hyano/pico-opm-writer/test/lfo_noise/result/wav_4a_01_am.tsv

file | mode | channel | sample_count | period_samples | cycle_count | confidence
wav_4a_01/am_nfrq_00_lfrq_00_kc_4a_mul_01.wav.zst | am | L | 7498868 | 262151.9194 | 28.6050 | 0.9948
wav_4a_01/am_nfrq_00_lfrq_01_kc_4a_mul_01.wav.zst | am | L | 7498868 | 262160.3223 | 28.6041 | 0.9950
wav_4a_01/am_nfrq_00_lfrq_02_kc_4a_mul_01.wav.zst | am | L | 7455437 | 262159.6877 | 28.4385 | 0.9949
wav_4a_01/am_nfrq_00_lfrq_03_kc_4a_mul_01.wav.zst | am | L | 7062996 | 262137.9389 | 26.9438 | 0.9949
wav_4a_01/am_nfrq_00_lfrq_04_kc_4a_mul_01.wav.zst | am | L | 6709862 | 262168.2118 | 25.5937 | 0.9949
wav_4a_01/am_nfrq_00_lfrq_05_kc_4a_mul_01.wav.zst | am | L | 6390348 | 262156.3210 | 24.3761 | 0.9950
wav_4a_01/am_nfrq_00_lfrq_06_kc_4a_mul_01.wav.zst | am | L | 6099892 | 262160.0876 | 23.2678 | 0.9950
wav_4a_01/am_nfrq_00_lfrq_07_kc_4a_mul_01.wav.zst | am | L | 5834681 | 262156.3415 | 22.2565 | 0.9949
wav_4a_01/am_nfrq_00_lfrq_08_kc_4a_mul_01.wav.zst | am | L | 5591530 | 262157.6165 | 21.3289 | 0.9950
wav_4a_01/am_nfrq_00_lfrq_09_kc_4a_mul_01.wav.zst | am | L | 5367877 | 262171.0440 | 20.4747 | 0.9950
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
