hyano/pico-opm-writer/test/lfo_noise/result/wav_4a_01_pm.tsv

file | mode | channel | sample_count | period_samples | cycle_count | confidence
wav_4a_01/pm_nfrq_00_lfrq_00_kc_4a_mul_01.wav.zst | pm | L | 7498867 | 262137.6661 | 28.6066 | 0.9910
wav_4a_01/pm_nfrq_00_lfrq_01_kc_4a_mul_01.wav.zst | pm | L | 7498867 | 262142.3183 | 28.6061 | 0.9905
wav_4a_01/pm_nfrq_00_lfrq_02_kc_4a_mul_01.wav.zst | pm | L | 7455435 | 262142.2755 | 28.4404 | 0.9905
wav_4a_01/pm_nfrq_00_lfrq_03_kc_4a_mul_01.wav.zst | pm | L | 7062993 | 262129.4264 | 26.9447 | 0.9868
wav_4a_01/pm_nfrq_00_lfrq_04_kc_4a_mul_01.wav.zst | pm | L | 6709856 | 262127.8747 | 25.5976 | 0.9906
wav_4a_01/pm_nfrq_00_lfrq_05_kc_4a_mul_01.wav.zst | pm | L | 6390348 | 262146.9127 | 24.3770 | 0.9892
wav_4a_01/pm_nfrq_00_lfrq_06_kc_4a_mul_01.wav.zst | pm | L | 6099892 | 262122.1143 | 23.2712 | 0.9888
wav_4a_01/pm_nfrq_00_lfrq_07_kc_4a_mul_01.wav.zst | pm | L | 5834682 | 262126.6337 | 22.2590 | 0.9898
wav_4a_01/pm_nfrq_00_lfrq_08_kc_4a_mul_01.wav.zst | pm | L | 5591531 | 262135.2868 | 21.3307 | 0.9909
wav_4a_01/pm_nfrq_00_lfrq_09_kc_4a_mul_01.wav.zst | pm | L | 5367877 | 262142.4000 | 20.4770 | 0.9900
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
