hyano/pico-opm-writer/test/lfo_noise/result/wav_am.tsv

file | mode | channel | sample_count | period_samples | cycle_count | confidence
wav/am_nfrq_00_lfrq_00_kc_4a_mul_04.wav.zst | am | L | 7498868 | 262137.4021 | 28.6066 | 0.9947
wav/am_nfrq_00_lfrq_01_kc_4a_mul_04.wav.zst | am | L | 7498868 | 262153.5946 | 28.6049 | 0.9950
wav/am_nfrq_00_lfrq_02_kc_4a_mul_04.wav.zst | am | L | 7455437 | 262135.8975 | 28.4411 | 0.9946
wav/am_nfrq_00_lfrq_03_kc_4a_mul_04.wav.zst | am | L | 7062996 | 262159.6973 | 26.9416 | 0.9948
wav/am_nfrq_00_lfrq_04_kc_4a_mul_04.wav.zst | am | L | 6709862 | 262164.9075 | 25.5941 | 0.9949
wav/am_nfrq_00_lfrq_05_kc_4a_mul_04.wav.zst | am | L | 6390348 | 262144.8821 | 24.3772 | 0.9949
wav/am_nfrq_00_lfrq_06_kc_4a_mul_04.wav.zst | am | L | 6099891 | 262163.5428 | 23.2675 | 0.9950
wav/am_nfrq_00_lfrq_07_kc_4a_mul_04.wav.zst | am | L | 5834682 | 262140.6615 | 22.2578 | 0.9949
wav/am_nfrq_00_lfrq_08_kc_4a_mul_04.wav.zst | am | L | 5591531 | 262159.3421 | 21.3287 | 0.9948
wav/am_nfrq_00_lfrq_09_kc_4a_mul_04.wav.zst | am | L | 5367877 | 262144.8064 | 20.4768 | 0.9947
wav/am_nfrq_00_lfrq_0a_kc_4a_mul_04.wav.zst | am | L | 5161471 | 262168.3591 | 19.6876 | 0.9949
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
