hyano/pico-opm-writer/test/lfo_noise/result/wav_lfrq28_am.tsv

file | mode | channel | sample_count | period_samples | cycle_count | confidence
wav_lfrq28/am_nfrq_00_lfrq_24_kc_4a_mul_04.wav.zst | am | L | 7498868 | 65536.2807 | 114.4232 | 0.9133
wav_lfrq28/am_nfrq_00_lfrq_25_kc_4a_mul_04.wav.zst | am | L | 7498867 | 65536.6209 | 114.4225 | 0.8626
wav_lfrq28/am_nfrq_00_lfrq_26_kc_4a_mul_04.wav.zst | am | L | 7498867 | 65536.7708 | 114.4223 | 0.8609
wav_lfrq28/am_nfrq_00_lfrq_27_kc_4a_mul_04.wav.zst | am | L | 7498867 | 65536.5741 | 114.4226 | 0.8626
wav_lfrq28/am_nfrq_00_lfrq_28_kc_4a_mul_04.wav.zst | am | L | 7498867 | 65536.7278 | 114.4224 | 0.8582
wav_lfrq28/am_nfrq_00_lfrq_29_kc_4a_mul_04.wav.zst | am | L | 7498868 | 65536.2855 | 114.4231 | 0.8591
wav_lfrq28/am_nfrq_00_lfrq_2a_kc_4a_mul_04.wav.zst | am | L | 7498868 | 65536.2191 | 114.4233 | 0.9086
wav_lfrq28/am_nfrq_00_lfrq_2b_kc_4a_mul_04.wav.zst | am | L | 7498867 | 65536.3893 | 114.4230 | 0.8583
wav_lfrq28/am_nfrq_00_lfrq_2c_kc_4a_mul_04.wav.zst | am | L | 7498868 | 65536.7194 | 114.4224 | 0.8617
wav_lfrq28/am_nfrq_1f_lfrq_24_kc_4a_mul_04.wav.zst | am | L | 7498867 | 65536.1403 | 114.4234 | 0.6660
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
