hyano/pico-opm-writer/src/stats.c

/*
 * 実行時リソース使用量の計測の実装
 *
 * SPDX-License-Identifier: MIT
 */
#include "stats.h"

#include "pico/stdlib.h"

/* ---- 1 秒窓管理 --------------------------------------------------------- */

static struct
{
    uint32_t window_start_us;  /* 現在の窓の開始時刻 [us] */
    uint32_t busy_us;          /* 窓内でサービス関数の中に居た時間 [us] */
    uint32_t usb_busy_us;      /* 窓内で tud_task() の中に居た時間 [us] */
    uint64_t frames_in_window; /* 窓内で追加されたフレーム数 */
    uint32_t passes_in_window; /* 窓内のメインループ周回数 */
} s_window = {
    .window_start_us = 0,
    .busy_us = 0,
    .usb_busy_us = 0,
    .frames_in_window = 0,
    .passes_in_window = 0,
};

/* 直近窓のメインループ周回数 [passes/s] */
static uint32_t s_loop_rate;

/* ---- サービスごとの実仕事率 -------------------------------------------- */

/* 窓の中の生カウント。窓が閉じたときに 1 秒あたりへ直して s_svc へ移す。 */
static struct
{
    uint32_t calls;
    uint32_t worked;
#if STATS_PROFILE
    uint32_t busy_us;
#endif
} s_svc_win[STATS_SVC_COUNT];

/* 直近窓の確定値 [回/s] */
static struct
{
    uint32_t calls;
    uint32_t worked;
#if STATS_PROFILE
    uint32_t busy_us;
#endif
} s_svc[STATS_SVC_COUNT];

/* `s` の 1 行に 6 個並べるので短くする */
static const char *const SVC_NAME[STATS_SVC_COUNT] = {
    [STATS_SVC_PCM8] = "pcm8",
    [STATS_SVC_CAPTURE] = "cap",
    [STATS_SVC_I2S] = "i2s",
    [STATS_SVC_VGM] = "vgm",
    [STATS_SVC_MDX] = "mdx",
    [STATS_SVC_STORAGE] = "sto",
};

void stats_svc_note(stats_svc_t svc, bool worked)
{
    s_svc_win[svc].calls++;
    if (worked)
    {
        s_svc_win[svc].worked++;
    }
}

#if STATS_PROFILE
void stats_svc_busy_add(stats_svc_t svc, uint32_t us)
{
    s_svc_win[svc].busy_us += us;
}

uint32_t stats_svc_busy_us(stats_svc_t svc)
{
    return s_svc[svc].busy_us;
}
#endif

uint32_t stats_svc_calls(stats_svc_t svc)
{
    return s_svc[svc].calls;
}

uint32_t stats_svc_worked(stats_svc_t svc)
{
    return s_svc[svc].worked;
}

const char *stats_svc_name(stats_svc_t svc)
{
    return SVC_NAME[svc];
}

/* 窓が閉じたときに 1 秒あたりへ直す。窓は 1 秒ちょうどとは限らない。 */
static void svc_close_window(uint32_t elapsed_us)
{
    for (uint32_t i = 0; i < (uint32_t)STATS_SVC_COUNT; i++)
    {
        s_svc[i].calls =
            (uint32_t)(((uint64_t)s_svc_win[i].calls * 1000000u) / elapsed_us);
        s_svc[i].worked =
            (uint32_t)(((uint64_t)s_svc_win[i].worked * 1000000u) / elapsed_us);
#if STATS_PROFILE
        s_svc[i].busy_us =
            (uint32_t)(((uint64_t)s_svc_win[i].busy_us * 1000000u) / elapsed_us);
#endif
        s_svc_win[i].calls = 0;
        s_svc_win[i].worked = 0;
#if STATS_PROFILE
        s_svc_win[i].busy_us = 0;
#endif
    }
}

/* 起動時と `s 0` で全部 0 に戻す */
static void svc_clear(void)
{
    for (uint32_t i = 0; i < (uint32_t)STATS_SVC_COUNT; i++)
    {
        s_svc_win[i].calls = 0;
        s_svc_win[i].worked = 0;
        s_svc[i].calls = 0;
        s_svc[i].worked = 0;
#if STATS_PROFILE
        s_svc_win[i].busy_us = 0;
        s_svc[i].busy_us = 0;
#endif
    }
}

/* ---- CPU 使用率 -------------------------------------------------------- */

static struct
{
    uint32_t cpu_percent;     /* 直近窓の CPU 使用率 [%] */
    uint32_t cpu_percent_max; /* リセット以降の最大値 [%] */
    uint32_t usb_percent;     /* 直近窓の tud_task() の占有率 [%] */
} s_cpu = {
    .cpu_percent = 0,
    .cpu_percent_max = 0,
    .usb_percent = 0,
};

/* ---- DMA リング -------------------------------------------------------- */

static struct
{
    uint32_t frames_current; /* 現在の未処理フレーム数 */
    uint32_t frames_max;     /* リセット以降の最大値 */
} s_ring = {
    .frames_current = 0,
    .frames_max = 0,
};

/* ---- USB TX ------------------------------------------------------------ */

static struct
{
    uint32_t bytes_current; /* 現在の滞留バイト数 */
    uint32_t bytes_max;     /* リセット以降の最大値 */
} s_usb_tx = {
    .bytes_current = 0,
    .bytes_max = 0,
};

/* ---- I2S 出力 ---------------------------------------------------------- */

/*
 * こちらは減る方向が危険なので low-water を残す。UINT32_MAX は「まだ 1 度も
 * 通知されていない」ことを表す番兵。
 */
static struct
{
    uint32_t depth_current; /* 現在の先行フレーム数 */
    uint32_t depth_min;     /* リセット以降の最小値 */
} s_i2s = {
    .depth_current = 0,
    .depth_min = UINT32_MAX,
};

/* ---- カウンタ ---------------------------------------------------------- */

static struct
{
    uint32_t overrun;      /* DMA overrun 発生回数 */
    uint64_t forbidden;    /* 禁止コード E=0 の検出数 */
    uint32_t rxstall;      /* PIO RX FIFO あふれ回数 */
    uint64_t frames;       /* 総フレーム数 */
    uint32_t frame_rate;   /* 直近窓でのフレームレート [frames/s] */
    uint32_t i2s_underrun; /* I2S の先行分が尽きた回数 */
    uint64_t pcm_clip;     /* ADPCM を混ぜた結果あふれたサンプル数 */
} s_counters = {
    .overrun = 0,
    .forbidden = 0,
    .rxstall = 0,
    .frames = 0,
    .frame_rate = 0,
    .i2s_underrun = 0,
    .pcm_clip = 0,
};

/* ---- フラッシュ書き込み / VGM ------------------------------------------ */

static struct
{
    uint32_t flash_write;           /* 4KiB ブロックの書き出し回数 */
    uint32_t flash_blackout_max_us; /* 書き出しでメインループが止まった最大時間 */
    uint32_t seq_lag_max_us;        /* シーケンサの遅れの最大値 */
    uint32_t loop_period_max_us;    /* service_all() の呼び出し間隔の最大値 */
    uint32_t audio_gap_max_us;      /* 音声チェーンが回った間隔の最大値 */
} s_ext = {
    .flash_write = 0,
    .flash_blackout_max_us = 0,
    .seq_lag_max_us = 0,
    .loop_period_max_us = 0,
    .audio_gap_max_us = 0,
};

/* ---- OPM バス（STATS_PROFILE のみ）------------------------------------- */

#if STATS_PROFILE
/* 窓の中の生カウント。窓が閉じたときに 1 秒あたりへ直して s_opm へ移す。 */
static struct
{
    uint32_t writes;
    uint32_t busy_us;
} s_opm_win;

static struct
{
    uint32_t writes;  /* 直近窓の書き込み回数 [writes/s] */
    uint32_t busy_us; /* 直近窓の滞在時間 [us/s] */
    uint32_t max_us;  /* リセット以降の 1 回の最大値 [us] */
} s_opm;
#endif

/* 起動時と `s 0` で 0 に戻す。STATS_PROFILE=0 では何も持たないので空になる。 */
static void opm_clear_stats(void)
{
#if STATS_PROFILE
    s_opm_win.writes = 0;
    s_opm_win.busy_us = 0;
    s_opm.writes = 0;
    s_opm.busy_us = 0;
    s_opm.max_us = 0;
#endif
}

/* ---- CPU 使用率 -------------------------------------------------------- */

void stats_busy_add(uint32_t busy_us)
{
    s_window.busy_us += busy_us;
}

void stats_usb_busy_add(uint32_t busy_us)
{
    s_window.usb_busy_us += busy_us;
}

void stats_service(void)
{
    s_window.passes_in_window++;

    uint32_t now_us = time_us_32();
    uint32_t elapsed_us = now_us - s_window.window_start_us;

    /* 1 秒 (1000000us) に満たなければ何もしない */
    if (elapsed_us < 1000000u)
    {
        return;
    }

    /* 窓が閉じた。統計を計算する。 */

    /* CPU 使用率を計算。窓は 1 秒ちょうどとは限らないので実経過時間で割る。 */
    uint32_t cpu_pct = (uint32_t)(((uint64_t)s_window.busy_us * 100u) / elapsed_us);
    if (cpu_pct > 100u)
    {
        cpu_pct = 100u;
    }
    s_cpu.cpu_percent = cpu_pct;

    /* 最大値を更新 */
    if (cpu_pct > s_cpu.cpu_percent_max)
    {
        s_cpu.cpu_percent_max = cpu_pct;
    }

    uint32_t usb_pct = (uint32_t)(((uint64_t)s_window.usb_busy_us * 100u) / elapsed_us);
    s_cpu.usb_percent = (usb_pct > 100u) ? 100u : usb_pct;

    /* フレームレートを計算（frames/s） */
    uint32_t frame_rate = (uint32_t)((s_window.frames_in_window * 1000000u) / elapsed_us);
    s_counters.frame_rate = frame_rate;

    /* メインループの周回数（1 周あたりの固定費を見積もるのに使う） */
    s_loop_rate = (uint32_t)(((uint64_t)s_window.passes_in_window * 1000000u) / elapsed_us);

    /* サービスごとの呼び出し回数と実仕事回数 */
    svc_close_window(elapsed_us);

#if STATS_PROFILE
    /* OPM バスも同じく 1 秒あたりへ直す（最大値は窓をまたいで残す） */
    s_opm.writes = (uint32_t)(((uint64_t)s_opm_win.writes * 1000000u) / elapsed_us);
    s_opm.busy_us = (uint32_t)(((uint64_t)s_opm_win.busy_us * 1000000u) / elapsed_us);
    s_opm_win.writes = 0;
    s_opm_win.busy_us = 0;
#endif

    /* 次の窓へ */
    s_window.window_start_us = now_us;
    s_window.busy_us = 0;
    s_window.usb_busy_us = 0;
    s_window.frames_in_window = 0;
    s_window.passes_in_window = 0;
}

uint32_t stats_loop_rate(void)
{
    return s_loop_rate;
}

uint32_t stats_usb_percent(void)
{
    return s_cpu.usb_percent;
}

uint32_t stats_cpu_percent(void)
{
    return s_cpu.cpu_percent;
}

uint32_t stats_cpu_percent_max(void)
{
    return s_cpu.cpu_percent_max;
}

/* ---- DMA リング -------------------------------------------------------- */

void stats_ring_update(uint32_t unread_frames)
{
    s_ring.frames_current = unread_frames;
    if (unread_frames > s_ring.frames_max)
    {
        s_ring.frames_max = unread_frames;
    }
}

uint32_t stats_ring_frames(void)
{
    return s_ring.frames_current;
}

uint32_t stats_ring_frames_max(void)
{
    return s_ring.frames_max;
}

/* ---- USB TX ------------------------------------------------------------ */

void stats_usb_tx_update(uint32_t pending_bytes)
{
    s_usb_tx.bytes_current = pending_bytes;
    if (pending_bytes > s_usb_tx.bytes_max)
    {
        s_usb_tx.bytes_max = pending_bytes;
    }
}

uint32_t stats_usb_tx_bytes(void)
{
    return s_usb_tx.bytes_current;
}

uint32_t stats_usb_tx_bytes_max(void)
{
    return s_usb_tx.bytes_max;
}

/* ---- I2S 出力 ---------------------------------------------------------- */

void __not_in_flash_func(stats_i2s_update)(uint32_t depth_frames)
{
    s_i2s.depth_current = depth_frames;
    if (depth_frames < s_i2s.depth_min)
    {
        s_i2s.depth_min = depth_frames;
    }
}

uint32_t stats_i2s_depth(void)
{
    return s_i2s.depth_current;
}

uint32_t stats_i2s_depth_min(void)
{
    return s_i2s.depth_min;
}

/* ---- カウンタ ---------------------------------------------------------- */

void stats_count_overrun(void)
{
    s_counters.overrun++;
}

void __not_in_flash_func(stats_count_forbidden)(uint32_t n)
{
    s_counters.forbidden += n;
}

void stats_count_rxstall(void)
{
    s_counters.rxstall++;
}

void stats_count_frames(uint32_t n)
{
    s_counters.frames += n;
    s_window.frames_in_window += n;
}

void __not_in_flash_func(stats_count_i2s_underrun)(void)
{
    s_counters.i2s_underrun++;
}

void __not_in_flash_func(stats_count_pcm_clip)(uint32_t n)
{
    s_counters.pcm_clip += n;
}

uint32_t stats_overrun(void)
{
    return s_counters.overrun;
}

uint64_t stats_forbidden(void)
{
    return s_counters.forbidden;
}

uint32_t stats_rxstall(void)
{
    return s_counters.rxstall;
}

uint64_t stats_frames(void)
{
    return s_counters.frames;
}

uint32_t stats_i2s_underrun(void)
{
    return s_counters.i2s_underrun;
}

uint64_t stats_pcm_clip(void)
{
    return s_counters.pcm_clip;
}

uint32_t stats_frame_rate(void)
{
    return s_counters.frame_rate;
}

/* ---- フラッシュ書き込み ------------------------------------------------ */

void stats_count_flash_write(void)
{
    s_ext.flash_write++;
}

void stats_flash_blackout_add(uint32_t us)
{
    if (us > s_ext.flash_blackout_max_us)
    {
        s_ext.flash_blackout_max_us = us;
    }
}

uint32_t stats_flash_write(void)
{
    return s_ext.flash_write;
}

uint32_t stats_flash_blackout_max_us(void)
{
    return s_ext.flash_blackout_max_us;
}

/* ---- シーケンサ再生 (VGM / MDX で共用) ---------------------------------- */

void stats_seq_lag_update(uint32_t us)
{
    if (us > s_ext.seq_lag_max_us)
    {
        s_ext.seq_lag_max_us = us;
    }
}

uint32_t stats_seq_lag_max_us(void)
{
    return s_ext.seq_lag_max_us;
}

/* ---- メインループの周期 ------------------------------------------------ */

void __not_in_flash_func(stats_loop_period_add)(uint32_t us)
{
    if (us > s_ext.loop_period_max_us)
    {
        s_ext.loop_period_max_us = us;
    }
}

void __not_in_flash_func(stats_audio_gap_add)(uint32_t us)
{
    if (us > s_ext.audio_gap_max_us)
    {
        s_ext.audio_gap_max_us = us;
    }
}

uint32_t stats_loop_period_max_us(void)
{
    return s_ext.loop_period_max_us;
}

uint32_t stats_audio_gap_max_us(void)
{
    return s_ext.audio_gap_max_us;
}

/* ---- OPM バス ---------------------------------------------------------- */

#if STATS_PROFILE
void stats_opm_write_add(uint32_t us)
{
    s_opm_win.writes++;
    s_opm_win.busy_us += us;
    if (us > s_opm.max_us)
    {
        s_opm.max_us = us;
    }
}

uint32_t stats_opm_writes(void)
{
    return s_opm.writes;
}

uint32_t stats_opm_write_us(void)
{
    return s_opm.busy_us;
}

uint32_t stats_opm_write_max_us(void)
{
    return s_opm.max_us;
}
#endif

/* ---- 初期化・リセット -------------------------------------------------- */

void stats_init(void)
{
    svc_clear();

    s_window.window_start_us = time_us_32();
    s_window.busy_us = 0;
    s_window.frames_in_window = 0;

    s_cpu.cpu_percent = 0;
    s_cpu.cpu_percent_max = 0;

    s_ring.frames_current = 0;
    s_ring.frames_max = 0;

    s_usb_tx.bytes_current = 0;
    s_usb_tx.bytes_max = 0;

    s_i2s.depth_current = 0;
    s_i2s.depth_min = UINT32_MAX;

    s_counters.overrun = 0;
    s_counters.forbidden = 0;
    s_counters.rxstall = 0;
    s_counters.frames = 0;
    s_counters.frame_rate = 0;
    s_counters.i2s_underrun = 0;
    s_counters.pcm_clip = 0;

    s_ext.flash_write = 0;
    s_ext.flash_blackout_max_us = 0;
    s_ext.seq_lag_max_us = 0;
    s_ext.loop_period_max_us = 0;
    s_ext.audio_gap_max_us = 0;

    opm_clear_stats();
}

void stats_reset(void)
{
    svc_clear();

    /* high-water / low-water とカウンタを初期値に戻す */
    s_cpu.cpu_percent_max = 0;
    s_ring.frames_max = 0;
    s_usb_tx.bytes_max = 0;
    s_i2s.depth_min = UINT32_MAX;

    s_counters.overrun = 0;
    s_counters.forbidden = 0;
    s_counters.rxstall = 0;
    s_counters.frames = 0;
    s_counters.frame_rate = 0;
    s_counters.i2s_underrun = 0;
    s_counters.pcm_clip = 0;

    s_ext.flash_write = 0;
    s_ext.flash_blackout_max_us = 0;
    s_ext.seq_lag_max_us = 0;
    s_ext.loop_period_max_us = 0;
    s_ext.audio_gap_max_us = 0;

    opm_clear_stats();

    /* 窓をリセット */
    s_window.window_start_us = time_us_32();
    s_window.busy_us = 0;
    s_window.frames_in_window = 0;
}
