hyano/pico-opm-writer/src/autoplay.h

/*
 * VGM / MDX の自動連続再生
 *
 * /VGM と /MDX のファイルを 1 本のプレイリストに束ね、曲の終わりを見張って次の曲へ
 * 送る。手で `vgm play` を打ち続ける代わりに、置いた曲を放っておいて鳴らすためのもの。
 *
 * **曲の終わり方そのものは songend.c が持つ。** ループ回数での打ち切りも、
 * フェードアウトも、終わったあとの余韻を待つのも向こうの仕事で、こちらは
 * songend_is_active() が落ちるのを待って次の曲へ送るだけ。曲間の無音は
 * 余韻が消えてから数え始まる。
 *
 * loop / fade はここにも設定があり、既定値が手動再生と違う（自動再生は 2 周で
 * フェード、手動は無限）。トラックを始めるたびに songend_arm() でこちらの値を
 * 渡して上書きする。
 *
 * SPDX-License-Identifier: MIT
 */
#ifndef AUTOPLAY_H
#define AUTOPLAY_H

#include <stdbool.h>
#include <stdint.h>

#ifndef AUTOPLAY_ENABLED
#define AUTOPLAY_ENABLED 1
#endif

/*
 * プレイリストの上限。/VGM と /MDX の合計。
 *
 * ルートからの相対パスを '\0' 区切りでプールへ詰める。8.3 の直下なら 12 バイト、
 * サブディレクトリを挟んでも数十バイトなので、24KB あれば 512 件はまず入る。
 * どちらかが先に尽きたら `# warn` を出して打ち切る。
 */
#define AUTOPLAY_MAX_ENTRIES 512u
#define AUTOPLAY_POOL_BYTES  24576u

/* 既定値。autoplay stop では消えず、電源投入時にここへ戻る。 */
#define AUTOPLAY_LOOP_DEFAULT    2u
#define AUTOPLAY_FADE_MS_DEFAULT 2000u
#define AUTOPLAY_GAP_MS_DEFAULT  2000u

/* loop / fade / gap の上限（`d <ms>` と同じ 10 進） */
#define AUTOPLAY_LOOP_MAX 99u
#define AUTOPLAY_MS_MAX   60000u

typedef enum
{
    AUTOPLAY_STOPPED = 0,
    AUTOPLAY_PLAYING, /* 曲を鳴らしている（songend の FADING / RINGOUT も含む） */
    AUTOPLAY_GAP,     /* 曲間の無音 */
} autoplay_state_t;

typedef enum
{
    AUTOPLAY_MODE_LIST = 0, /* 一覧の順 */
    AUTOPLAY_MODE_RANDOM,   /* シャッフル */
} autoplay_mode_t;

typedef enum
{
    AUTOPLAY_SOURCE_BOTH = 0,
    AUTOPLAY_SOURCE_VGM,
    AUTOPLAY_SOURCE_MDX,
} autoplay_source_t;

/* ---- 初期化とサービス -------------------------------------------------- */

void autoplay_init(void);

/*
 * メインループから呼ぶ。曲の終わり・ループ回数・フェードと間隔の期限を見て
 * 状態を進める。戻り値は実仕事をしたかどうか。
 *
 * vgm_service() / mdx_service() より後に呼ぶこと。同じ周回で更新された再生状態を
 * そのまま見られる。
 */
bool autoplay_service(void);

/* ---- 操作 -------------------------------------------------------------- */

/*
 * プレイリストを作り直して 1 曲目を鳴らす（開始時は間隔を空けない）。
 * 成功なら NULL、失敗ならエラー理由の文字列（vgm_play() と同じ流儀）。
 */
const char *autoplay_start(void);

/*
 * 自動再生を止める。鳴っている曲も止めて出力ゲインを戻す。冪等。
 *
 * 手で `vgm play` / `mdx play` / `*_stop` を打ったときにも呼ぶ。走っていたときだけ
 * 通知を出す。
 */
const char *autoplay_stop(void);

/* 次 / 前の曲へ即座に移る。フェードも間隔も挟まない。停止中なら "wrong state"。 */
const char *autoplay_skip(int dir);

/* ---- 設定 -------------------------------------------------------------- */

/* 実行中に変えてもよい。次の判定から効く。 */
void autoplay_set_mode(autoplay_mode_t mode);
void autoplay_set_source(autoplay_source_t source);
void autoplay_set_loop(uint32_t loops); /* 0 = 無限（自然終了でだけ曲を送る） */
void autoplay_set_fade_ms(uint32_t ms); /* 0 = フェードせず即停止 */
void autoplay_set_gap_ms(uint32_t ms);  /* 0 = 間隔なし */

autoplay_mode_t autoplay_mode(void);
autoplay_source_t autoplay_source(void);
uint32_t autoplay_loop(void);
uint32_t autoplay_fade_ms(void);
uint32_t autoplay_gap_ms(void);

/* ---- 問い合わせ -------------------------------------------------------- */

autoplay_state_t autoplay_state(void);
const char *autoplay_state_name(void);

/* 停止していない（PLAYING / FADING / GAP のいずれか）。曲間でも true。 */
bool autoplay_is_running(void);

const char *autoplay_mode_name(void);
const char *autoplay_source_name(void);

uint32_t autoplay_count(void);    /* プレイリストの件数 */
uint32_t autoplay_position(void); /* 1 始まりの現在位置。停止中は 0 */

const char *autoplay_current_name(void); /* 現在の曲名。無ければ空文字列 */
bool autoplay_current_is_vgm(void);

/* プレイリストを 1 行ずつ出力する。tick は 1 行ごと（vgm_list() と同じ理由）。 */
const char *autoplay_print_list(void (*tick)(void));

#endif /* AUTOPLAY_H */
